thermseekr/eumesmo-io-24v16ch/oldversions/V5/esp-24v-16ch-v5.2.0.png

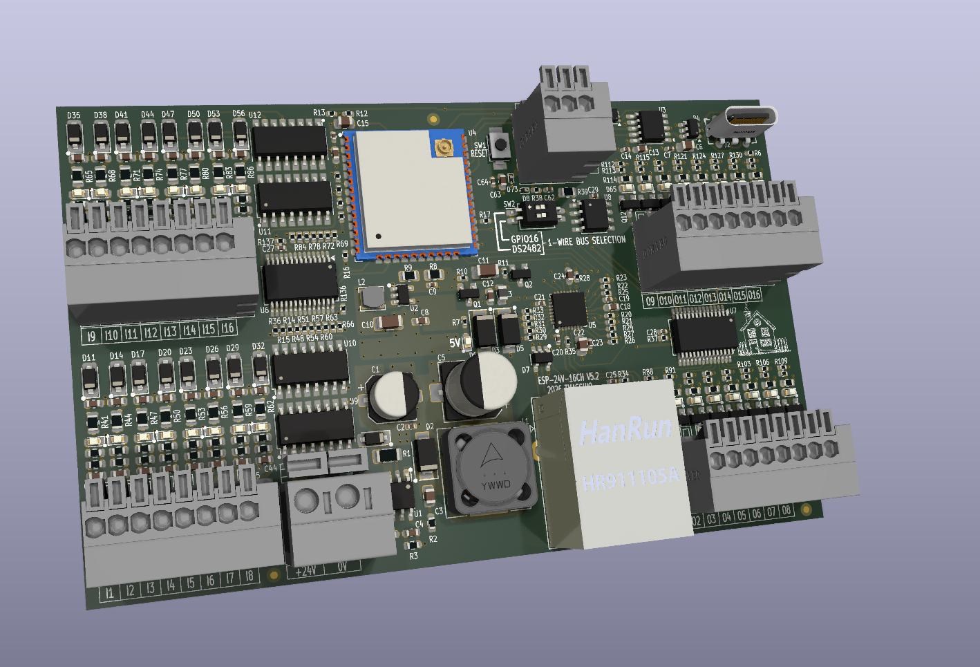
oldversions/V5/esp-24v-16ch-v5.2.0.png
